apoluekt/OpenRPNCalc/Code/Raylib/resources/panel.png

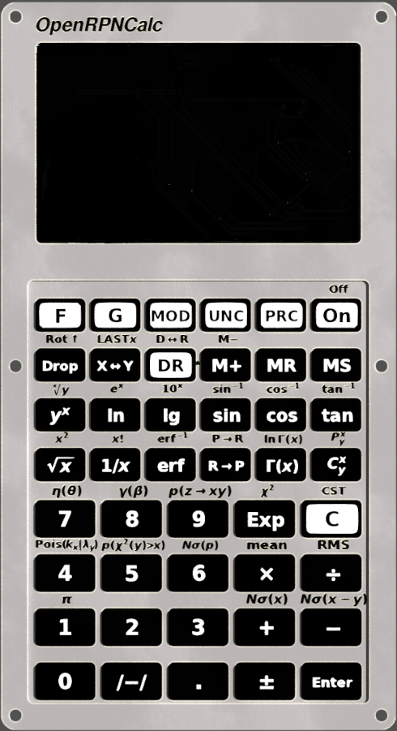
Code/Raylib/resources/panel.png
