apoluekt/OpenRPNCalc/Code/Core/Src/sharp.c

/*
 * sharp.c
 *
 * Functions to work with Sharp Memory LCD of type LS027B7DH01.
 *
 * The display in OpenRPNCalc is installed upside down for convenience of PCB routing,
 * so this has to be taken into account in the firmware.
 *
 *  Created on: Mar 9, 2021
 *      Author: apolu
 */

#include "stm32u3xx_hal.h"
#include "fonts.h"
#include "sharp.h"

/* String buffer (maximum 64 pixels high) */
uint8_t buffer[BUFFER_SIZE];

TIM_HandleTypeDef* _htim1;
SPI_HandleTypeDef* _hspi2;

/* Microsecond delay */
void delay_us (uint16_t us)
{
	__HAL_TIM_SET_COUNTER(_htim1,0);  // set the counter value a 0
	while (__HAL_TIM_GET_COUNTER(_htim1) < us);  // wait for the counter to reach the us input in the parameter
}

/* Clear display */
void sharp_clear() {
	uint8_t b[2] = {0x04, 0x00};
	HAL_GPIO_WritePin(GPIOC, GPIO_PIN_0, GPIO_PIN_SET);
	delay_us(12);
	HAL_SPI_Transmit(_hspi2, b, 2, 100);
	delay_us(4);
	HAL_GPIO_WritePin(GPIOC, GPIO_PIN_0, GPIO_PIN_RESET);
	delay_us(4);
}

/* Initialise display: start timers, send "ON" signal, and call clear function.  */
void sharp_init(TIM_HandleTypeDef* htim1, SPI_HandleTypeDef* hspi2) {
    _htim1 = htim1;
    _hspi2 = hspi2;

	HAL_TIM_Base_Start(_htim1); // Start microsecond timer

	delay_us(30);
	HAL_GPIO_WritePin(GPIOA, GPIO_PIN_10, GPIO_PIN_SET);  // DISP signal to "ON"
	delay_us(30);
	sharp_clear();
}

/* Send the string buffer content to the display via SPI interface.
 *   y : vertical coordinate of the top pixel of the string (0...239)
 *   lines : number of lines to send from the buffer (up to 64)
 */
void sharp_send_buffer(uint16_t y, uint16_t lines) {
    buffer[0] = 0x01;
    uint16_t size = (3+lines*52);
    for (int j=0; j<lines; j++) {
		if (y+j<240) buffer[j*52+1] = (uint8_t)(y+j+1);
    }
	HAL_GPIO_WritePin(GPIOC, GPIO_PIN_0, GPIO_PIN_SET);
	delay_us(12);
	HAL_SPI_Transmit(_hspi2, buffer, size, 100);
	delay_us(4);
	HAL_GPIO_WritePin(GPIOC, GPIO_PIN_0, GPIO_PIN_RESET);
	delay_us(4);
}

void sharp_clear_buffer(uint16_t lines, unsigned char value) {
	size_t size = (2+lines*52);
	memset(buffer, value, size);
}

void sharp_invert_buffer(uint16_t lines) {
	size_t size = (2+lines*52);
	for (size_t i=0; i<size; i++) {
		buffer[i] ^= 0xFF;
	}
}

/* Draw string in the string buffer (without sending it to screen).
 *   str : string to be drawn
 *   font: pointer to the font structure
 *   dx: x coordinate of the start of the string
 *   dy: y coordinate of the start of the string in the buffer
 *       (keep in mind that the buffer itself can be drawn at the arbitrary
 *       location later in the call to sharp_send_buffer(). )
 *   */
void sharp_string(char* str, FontDef_t *font, uint16_t dx, uint16_t dy) {
    uint16_t width = font->FontWidth;
    uint16_t height = font->FontHeight;
    uint16_t bytes = (width+7)/8;
    const char (*data)[bytes*height] = font->data;
    uint16_t xpos = dx;
    uint16_t dy52 = dy*52;
    int i=0;

    union {
      uint16_t word;
      uint8_t byte[2];
    } split_word;

    if (height+dy > BUFFER_LINES) height = BUFFER_LINES-dy;

    while (xpos<400) {
        uint8_t c = str[i];
        if(c == 0x00) break;
        const char *cdata = data[c];
        uint16_t xaddr = xpos>>3;
        uint16_t xshift = xpos & 0x0007;
        uint16_t jdy52 = 2+dy52;
        uint16_t faddr = 0;
        for (uint16_t j=0; j<height; j++) {
            uint16_t xaddrb = jdy52 + xaddr;
            jdy52 += 52;
            for (uint16_t b=0; b<bytes; b++) {
            	split_word.word = (uint8_t)cdata[faddr];
                split_word.word <<= xshift;
            	if (xaddrb < jdy52) buffer[xaddrb] &= ~split_word.byte[0];
            	xaddrb++;
            	if (xaddrb < jdy52) buffer[xaddrb] &= ~split_word.byte[1];
            	faddr++;
            }
        }
        xpos += width;
        i++;
    }
}

void sharp_char(uint8_t c, FontDef_t *font, uint16_t dx, uint16_t dy) {
    uint16_t width = font->FontWidth;
    uint16_t height = font->FontHeight;
    uint16_t bytes = (width+7)/8;
    const char (*data)[bytes*height] = font->data;
    uint16_t dy52 = dy*52;
    union {
      uint16_t word;
      uint8_t byte[2];
    } split_word;

    if (height+dy > BUFFER_LINES) height = BUFFER_LINES-dy;
    const char *cdata = data[c];
    uint16_t xaddr = dx>>3;
    uint16_t xshift = dx & 0x0007;
    uint16_t jdy52 = 2+dy52;
    uint16_t faddr = 0;
    for (uint16_t j=0; j<height; j++) {
        uint16_t xaddrb = jdy52 + xaddr;
        jdy52 += 52;
        for (uint16_t b=0; b<bytes; b++) {
          	split_word.word = (uint8_t)cdata[faddr];
            split_word.word <<= xshift;
          	if (xaddrb < jdy52) buffer[xaddrb] &= ~split_word.byte[0];
           	xaddrb++;
           	if (xaddrb < jdy52) buffer[xaddrb] &= ~split_word.byte[1];
           	faddr++;
        }
    }
}

void sharp_string_fast_16x26(char* str, uint8_t col, uint8_t dy) {
	FontDef_t* font = &font_16x26;
	uint8_t height = font->FontHeight;
	const char (*data)[2*height] = font->data;
	uint8_t c = col;
	int i=0;
    if (height+dy > BUFFER_LINES) height = BUFFER_LINES-dy;
    uint16_t dy52 = dy*52;
	while (c<50) {
        uint8_t ch = str[i];
        if(ch == 0x00) break;
        const char *cdata = data[ch];
        uint16_t xaddr = dy52 + 2 + c;
        uint8_t j2 = 0;
        for (uint8_t j=0; j<height; j++) {
            buffer[xaddr] = ~cdata[j2++];
            buffer[xaddr+1] = ~cdata[j2++];
            xaddr += 52;
        }
        i++;
        c+=2;
	}
}

void sharp_char_fast_16x26(uint8_t ch, uint8_t col, uint8_t dy) {
	FontDef_t* font = &font_16x26;
	uint8_t height = font->FontHeight;
	const char (*data)[2*height] = font->data;
    if (height+dy > BUFFER_LINES) height = BUFFER_LINES-dy;
    const char *cdata = data[ch];
    uint16_t xaddr = dy*52 + 2 + col;
    uint8_t j2 = 0;
    for (uint8_t j=0; j<height; j++) {
        buffer[xaddr] = ~cdata[j2++];
        buffer[xaddr+1] = ~cdata[j2++];
        xaddr += 52;
    }
}

void sharp_string_fast_24x40(char* str, uint8_t col, uint8_t dy) {
	FontDef_t* font = &font_24x40;
	uint8_t height = font->FontHeight;
	const char (*data)[3*height] = font->data;
	uint8_t c = col;
	int i=0;
    if (height+dy > BUFFER_LINES) height = BUFFER_LINES-dy;
    uint16_t dy52 = dy*52;
	while (c<50) {
        uint8_t ch = str[i];
        if(ch == 0x00) break;
        const char *cdata = data[ch];
        uint16_t xaddr = dy52 + 2 + c;
    	uint8_t j3 = 0;
        for (uint8_t j=0; j<height; j++) {
            buffer[xaddr] = ~cdata[j3++];
            buffer[xaddr+1] = ~cdata[j3++];
            buffer[xaddr+2] = ~cdata[j3++];
            xaddr += 52;
        }
        i++;
        c+=3;
	}
}

void sharp_char_fast_24x40(uint8_t ch, uint8_t col, uint8_t dy) {
	FontDef_t* font = &font_24x40;
	uint8_t height = font->FontHeight;
	const char (*data)[3*height] = font->data;
    if (height+dy > BUFFER_LINES) height = BUFFER_LINES-dy;
    const char *cdata = data[ch];
    uint16_t xaddr = dy*52 + 2 + col;
    uint8_t j3 = 0;
    for (uint8_t j=0; j<height; j++) {
        buffer[xaddr] = ~cdata[j3++];
        buffer[xaddr+1] = ~cdata[j3++];
        buffer[xaddr+2] = ~cdata[j3++];
        xaddr += 52;
    }
}

// Draws a filled rectangle in a monochrome buffer.
// Parameters:
// - dx: X-coordinate of the top-left corner of the rectangle.
// - dy: Y-coordinate of the top-left corner of the rectangle.
// - width: Width of the rectangle in pixels.
// - height: Height of the rectangle in pixels.
// - color: 1 for white, 0 for black, any other value for invert
void sharp_filled_rectangle(size_t dx, size_t dy, size_t width, size_t height,
                           uint8_t color) {
    int x = dx;
    int y = dy;
    if (width == 0 || height == 0) return;

    // Limit the rectangle to the buffer boundaries
    size_t max_x = x + width + 1 > BUFFER_WIDTH ? BUFFER_WIDTH : x + width + 1;
    size_t max_y = y + height > BUFFER_LINES ? BUFFER_LINES : y + height;

    size_t start_offset = x % 8;
    size_t end_offset = max_x % 8;

    for (size_t row = y; row < max_y; row++) {
        size_t start_byte = row*52 + x / 8 + 2;
        size_t end_byte = row*52 + (max_x - 1) / 8 + 2;

        // Handle the first partial byte if necessary
        if (start_byte == end_byte) {
            uint8_t mask = (((uint8_t)0xFF << start_offset) & ((uint8_t)0xFF >> (8 - end_offset)));
            if (color == 0) {
                buffer[start_byte] &= ~mask;
            } else if (color == 1) {
                buffer[start_byte] |= mask;
            } else {
                buffer[start_byte] ^= mask;
            }
        } else {
            if (start_offset != 0) {
                uint8_t start_mask = ((uint8_t)0xFF << start_offset);
                if (color == 0) {
                    buffer[start_byte] &= ~start_mask;
                } else if (color == 1) {
                    buffer[start_byte] |= start_mask;
                } else {
                    buffer[start_byte] ^= start_mask;
                }
                start_byte++;
            }

            // Fill whole bytes in between
            for (size_t byte = start_byte; byte < end_byte; byte++) {
                buffer[byte] = color ? 0xFF : 0x00;
            }

            // Handle the last partial byte if necessary
            if (end_offset != 0) {
                uint8_t end_mask = (0xFF >> (8 - end_offset));
                if (color == 0) {
                    buffer[end_byte] &= ~end_mask;
                } else if (color == 1) {
                    buffer[end_byte] |= end_mask;
                } else {
                    buffer[end_byte] ^= end_mask;
                }
            }
        }
    }
}


void sharp_test_font(FontDef_t *font, char start_symbol) {
	int w, h;
	if (font == NULL) {
		w = 16;
		h = 26;
	} else {
	    w = font->FontWidth;
	    h = font->FontHeight;
	}
	int rows = 240/h;
	int columns = 400/w;
	char str[67];
	char symbol = start_symbol;
	sharp_clear();
	for (int r=0; r<rows; r++) {
		for (int c=0; c<columns; c++) {
			str[c] = (symbol == 0 ? ' ' : symbol);
			symbol++;
		}
		str[columns] = 0x00;
		memset(buffer, 0xFF, 2+h*52);
		if (font) sharp_string(str, font, 0, 0);
		else sharp_string_fast_16x26(str, 0, 0);
		sharp_send_buffer(r*h, h);
	}
}
